YogangSingh/catamaran_shu_vFimal/USV2 Test Data/Test 2.png

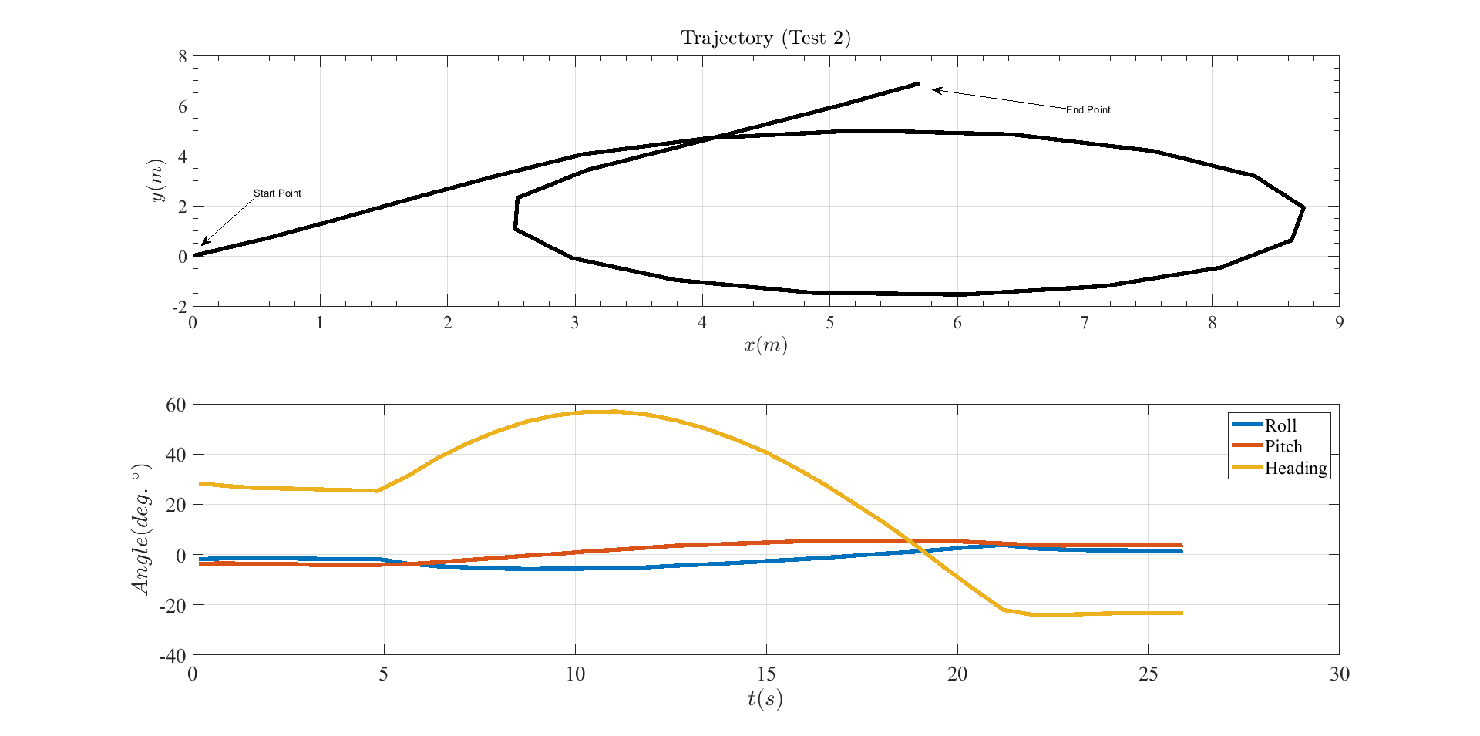
USV2 Test Data/Test 2.png
